fgervais/usbarm/Planning/deviceConnected.png

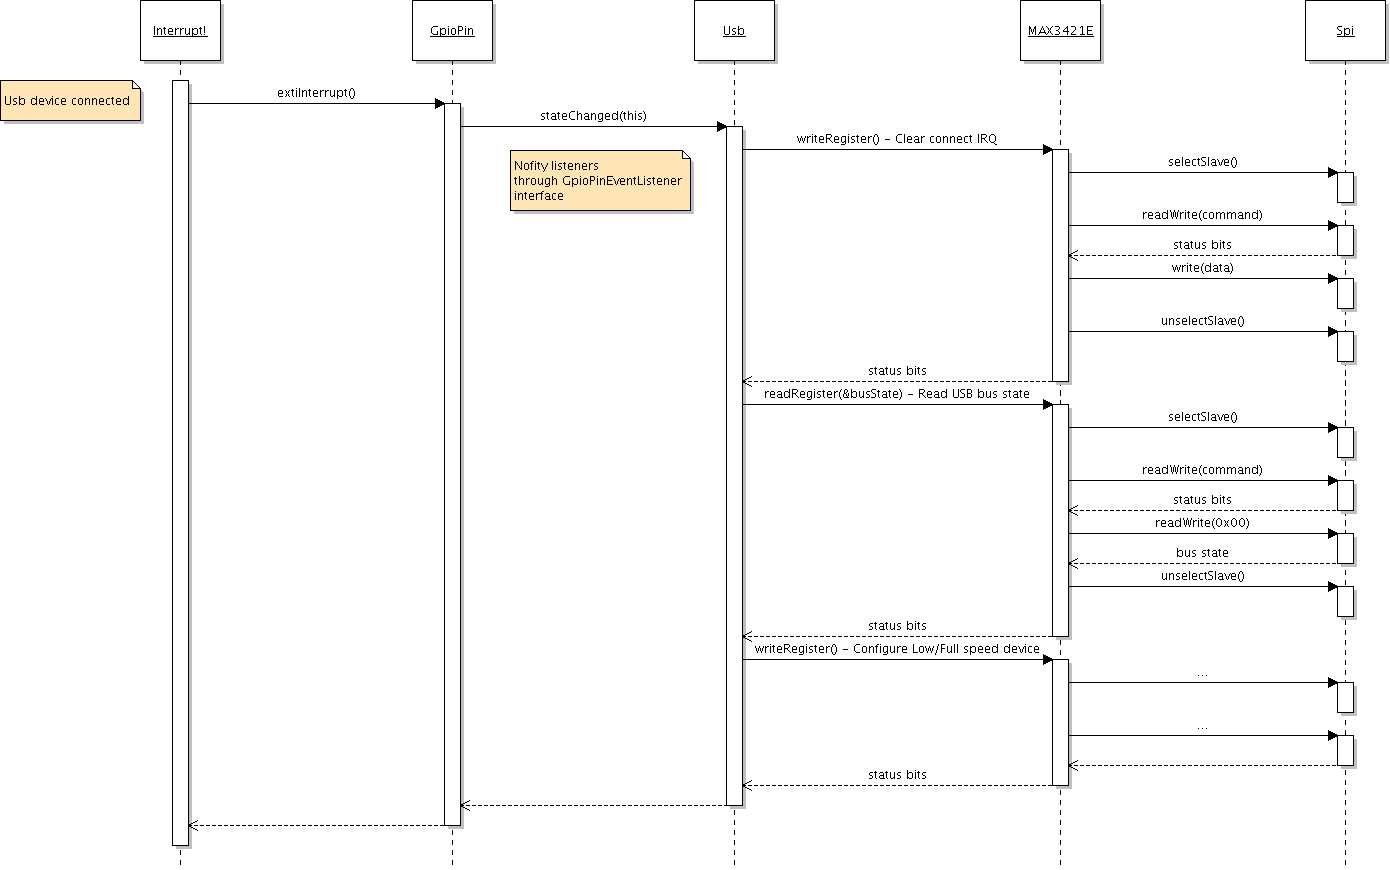
Planning/deviceConnected.png
