fgervais/usbarm/Planning/Framework_layer.png

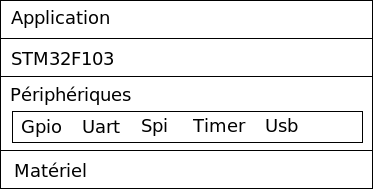
Planning/Framework_layer.png
