fgervais/usbarm/Planning/framework_led.png

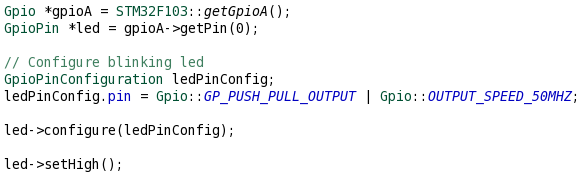
Planning/framework_led.png
