fgervais/usbarm/Planning/gantt-1dec2009.png

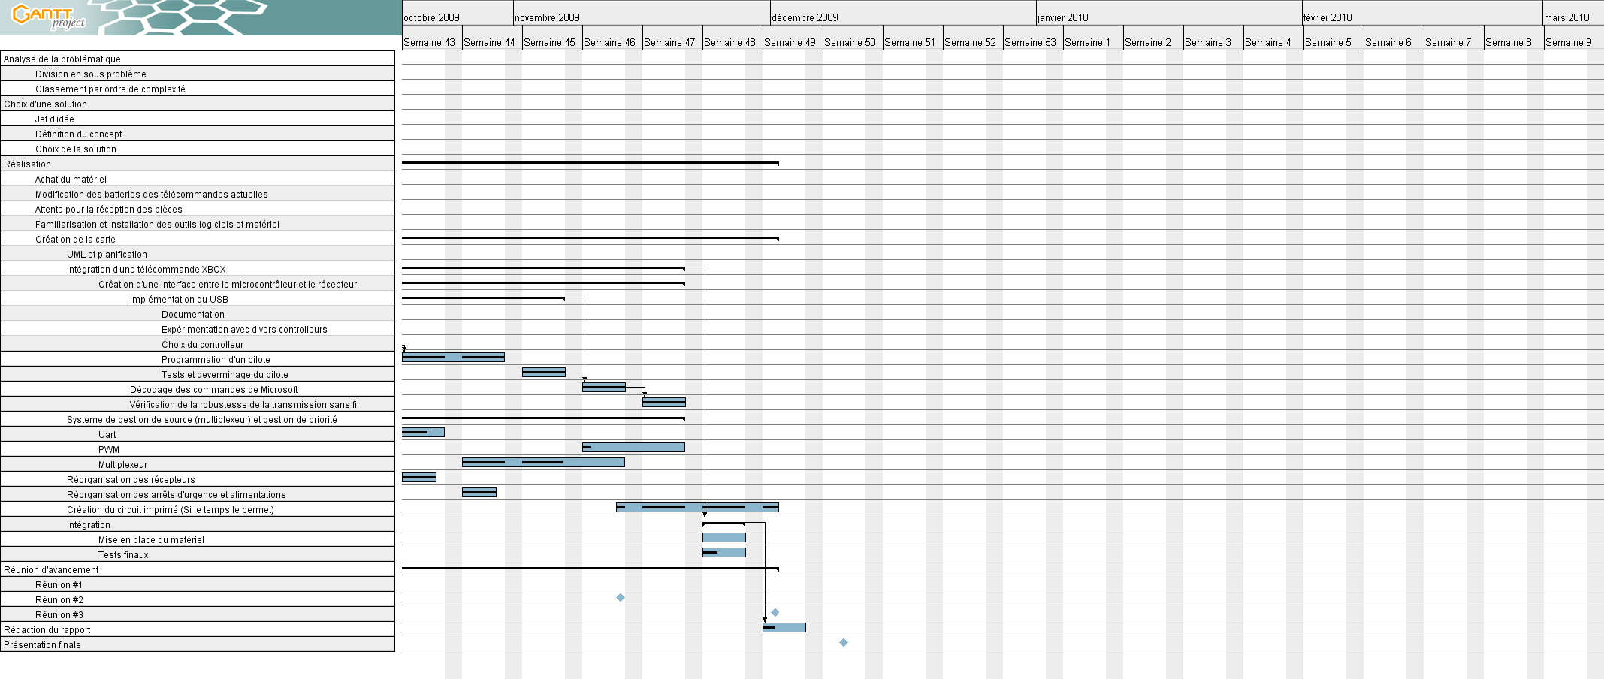
Planning/gantt-1dec2009.png
