fgervais/usbarm/Planning/gantt.png

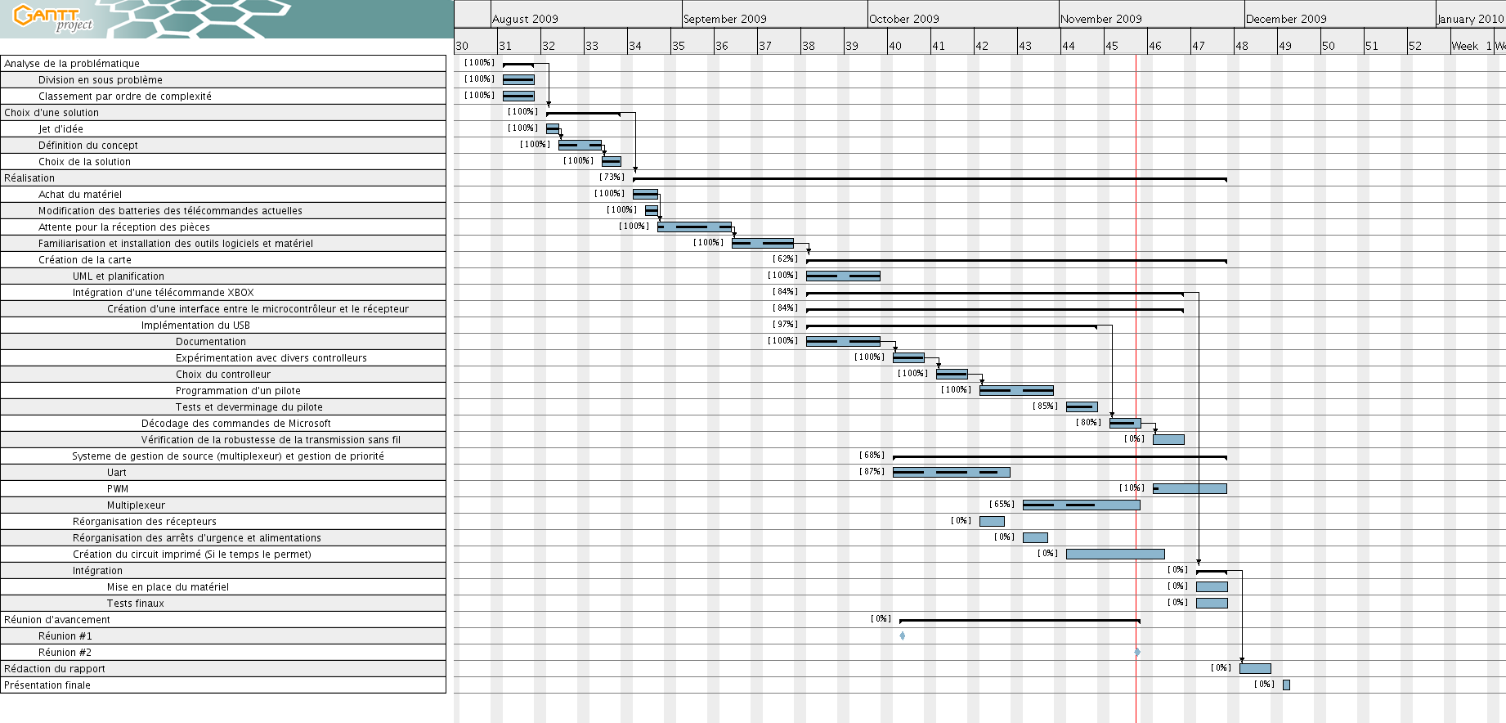
Planning/gantt.png
