fgervais/usbarm/Planning/listenForDevice.png

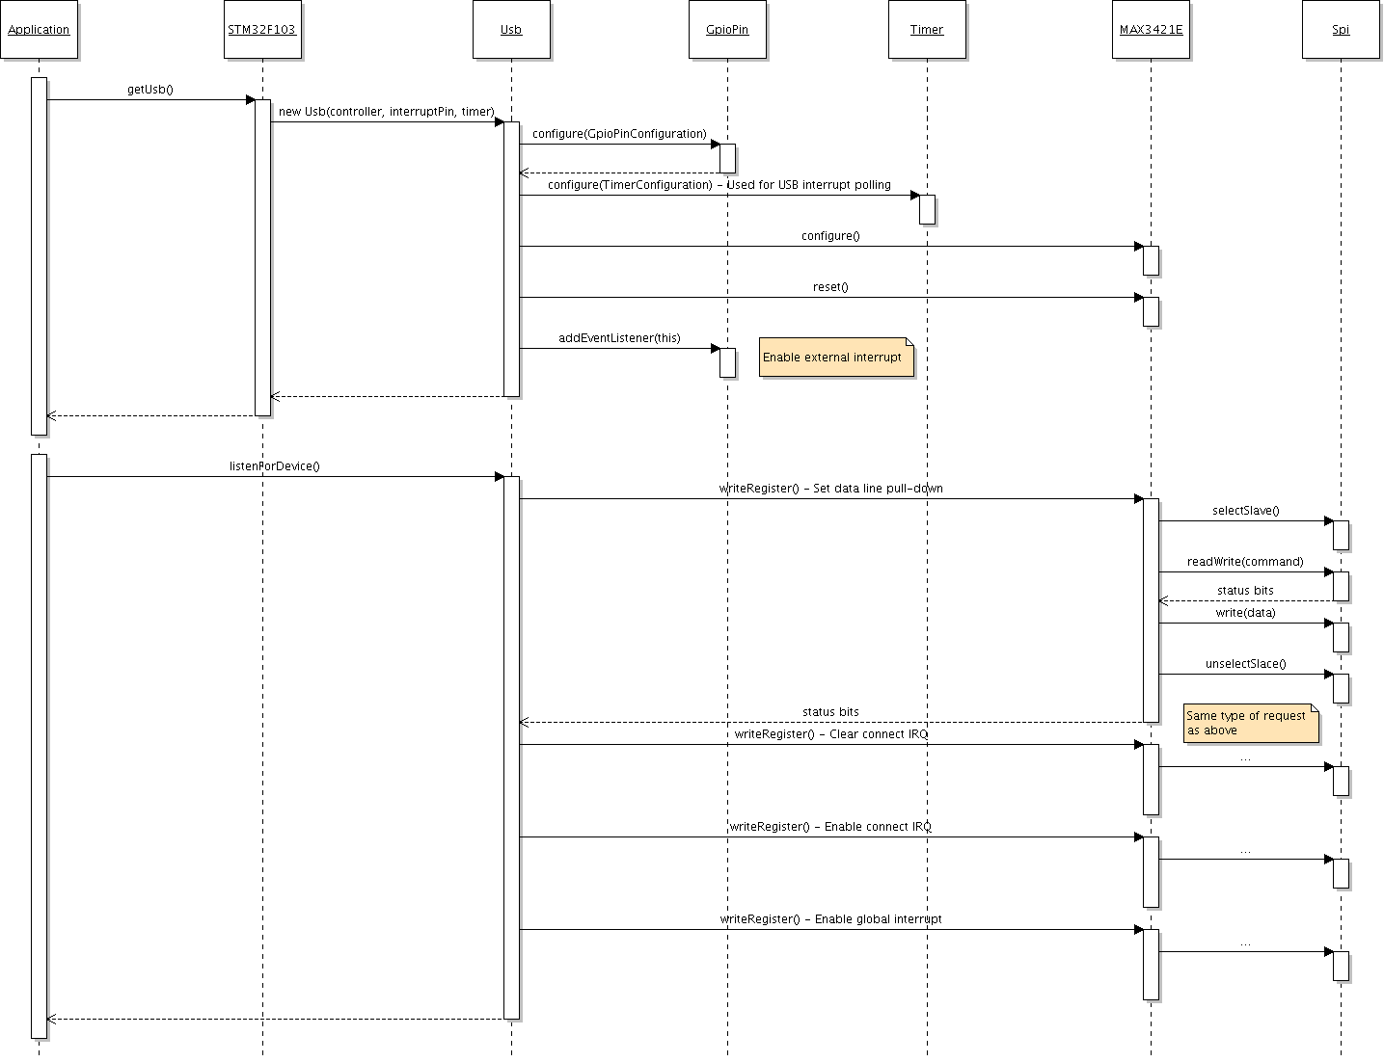
Planning/listenForDevice.png
