fgervais/usbarm/Planning/NES-i-Xbox-360-495x367.jpg

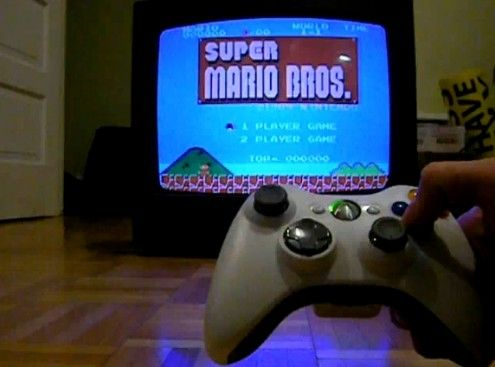
Planning/NES-i-Xbox-360-495x367.jpg
