fgervais/usbarm/Planning/timer_eventlistener.png

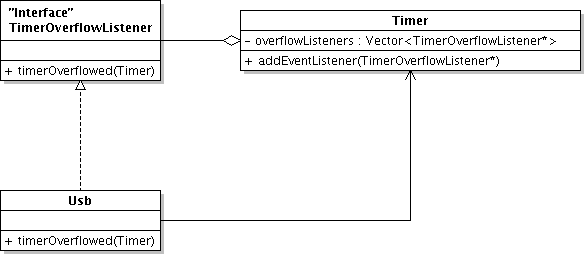
Planning/timer_eventlistener.png
