fgervais/usbarm/Planning/UML.violet.png

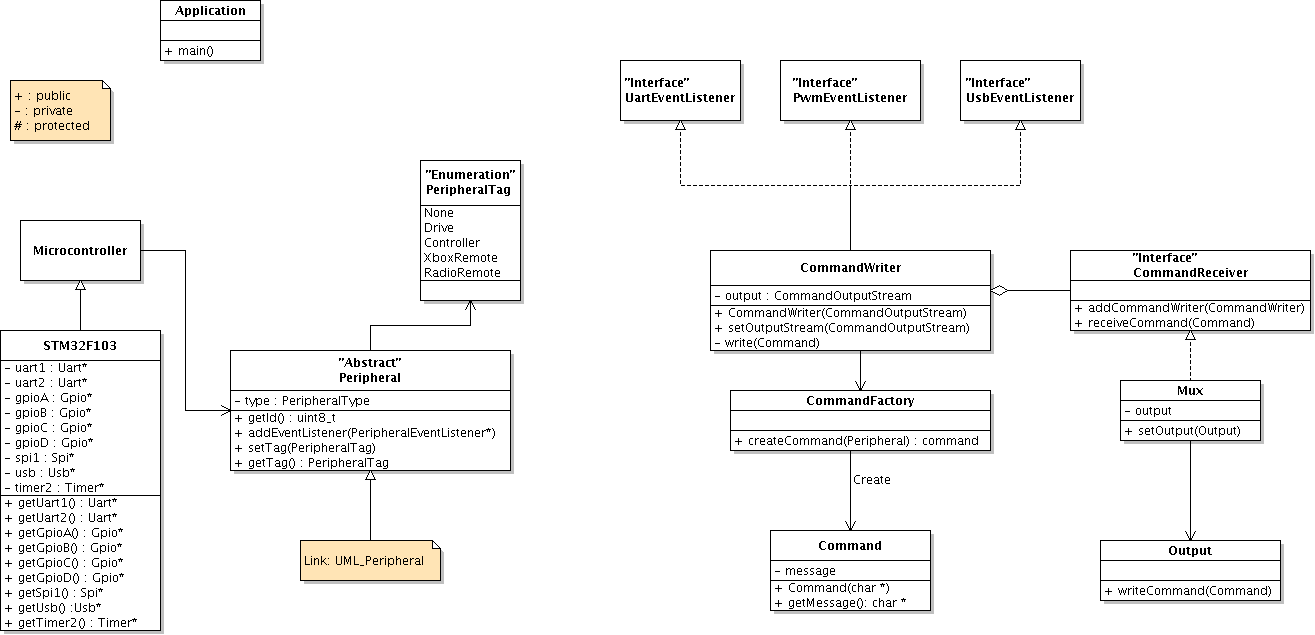
Planning/UML.violet.png
