fgervais/usbarm/Planning/UML_Peripheral.png

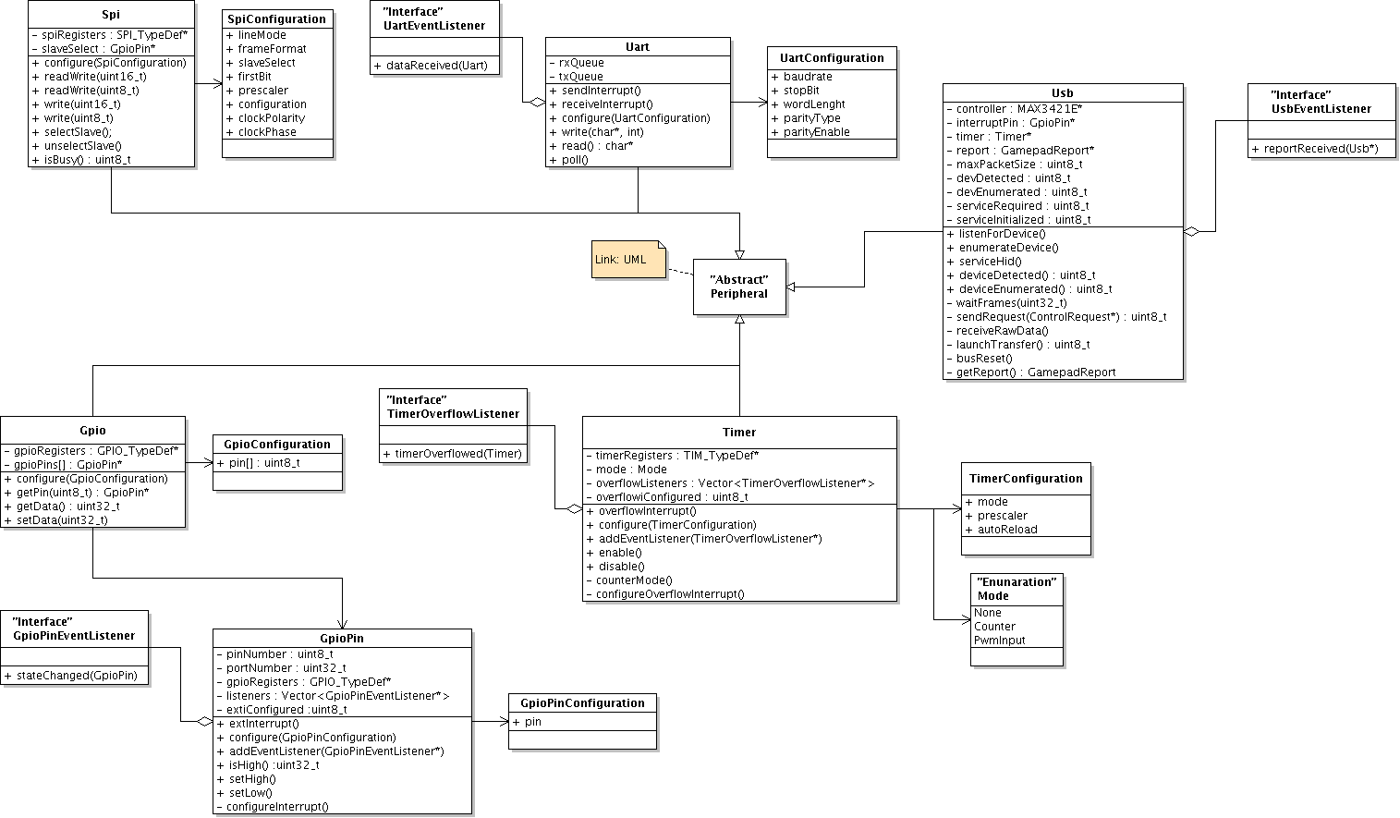
Planning/UML_Peripheral.png
