fgervais/usbarm/Planning/UML_USB.png

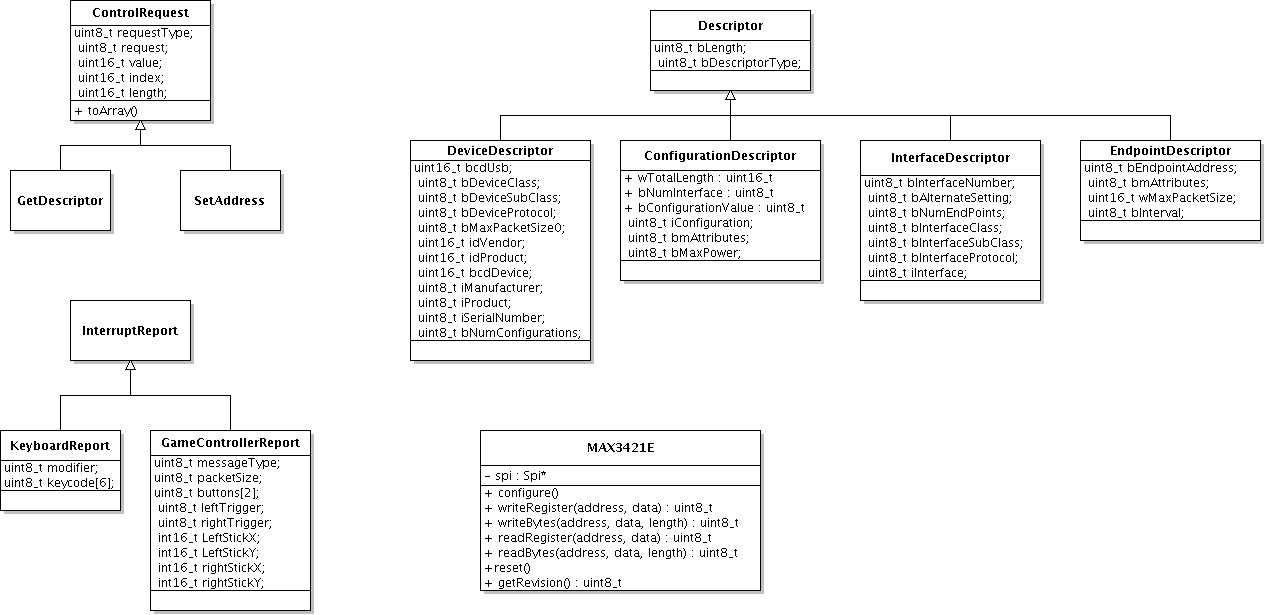
Planning/UML_USB.png
