fgervais/usbarm/Planning/USB_layer.png

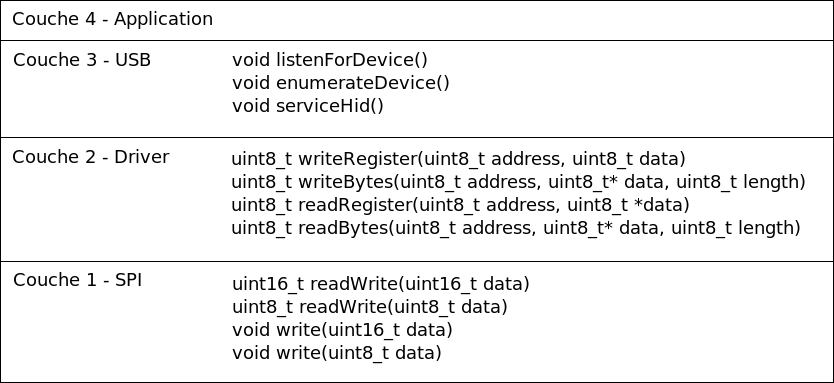
Planning/USB_layer.png
