fgervais/usbarm/Rapport/getReport_time_64.png

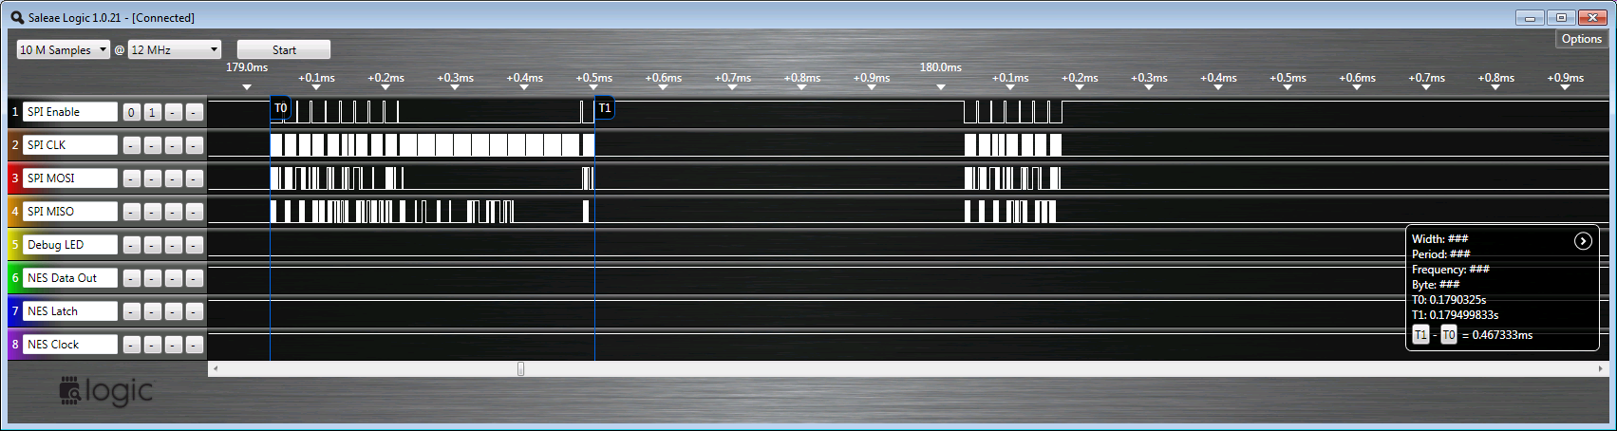
Rapport/getReport_time_64.png
