fgervais/usbarm/Rapport/getReport_time_256.png

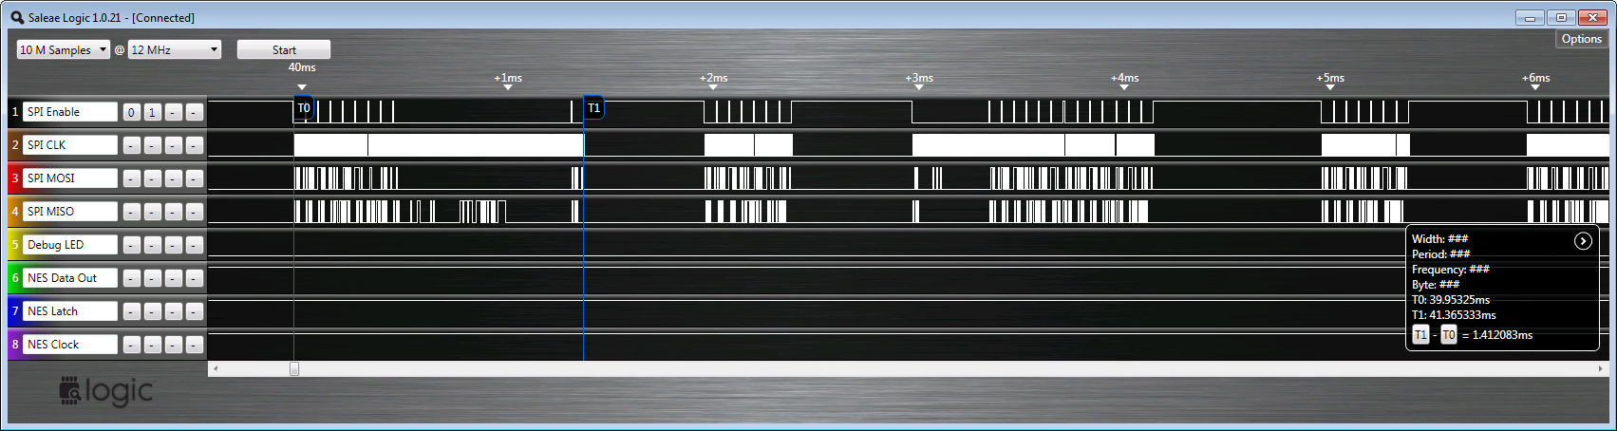
Rapport/getReport_time_256.png
