fgervais/usbarm/Rapport/getReport_time_analysis3.png

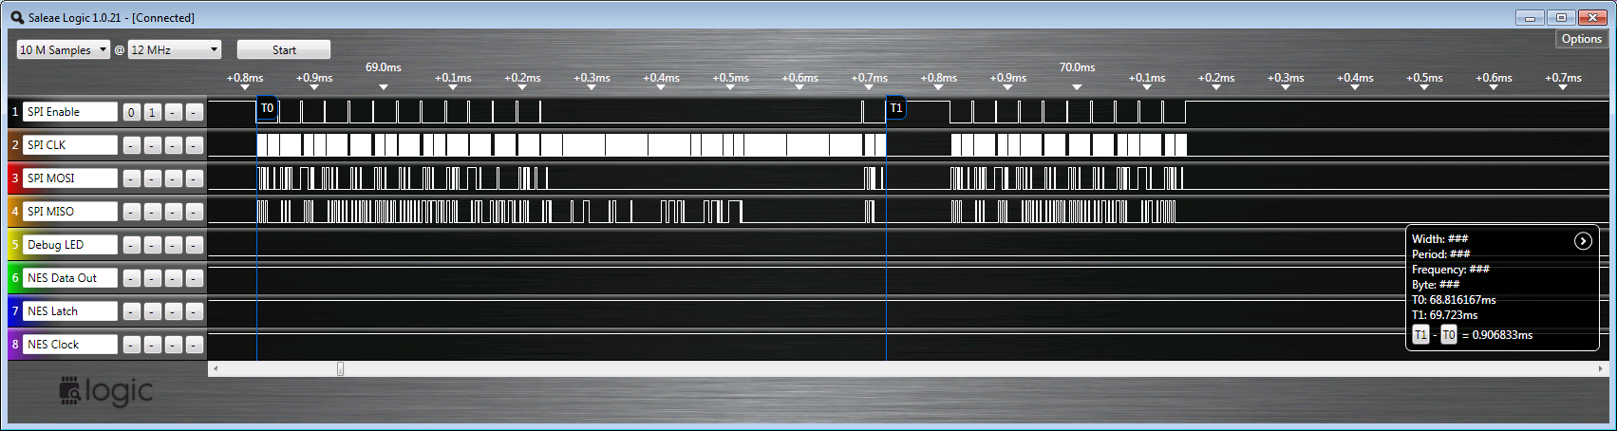
Rapport/getReport_time_analysis3.png
