fgervais/usbarm/Rapport/images/41DaZn46LVL._SL500_AA280_.jpg

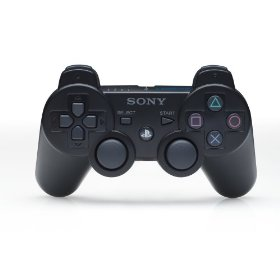
Rapport/images/41DaZn46LVL._SL500_AA280_.jpg
