fgervais/usbarm/Rapport/images/CapraPowerPointbgCapra.png

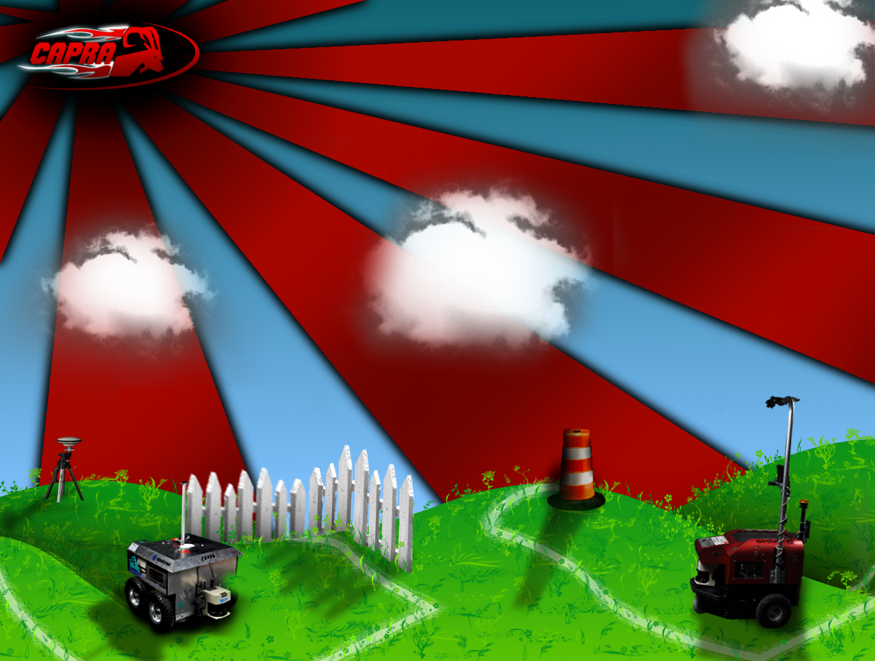
Rapport/images/CapraPowerPointbgCapra.png
