fgervais/usbarm/Rapport/images/CapraPowerPointFront.png

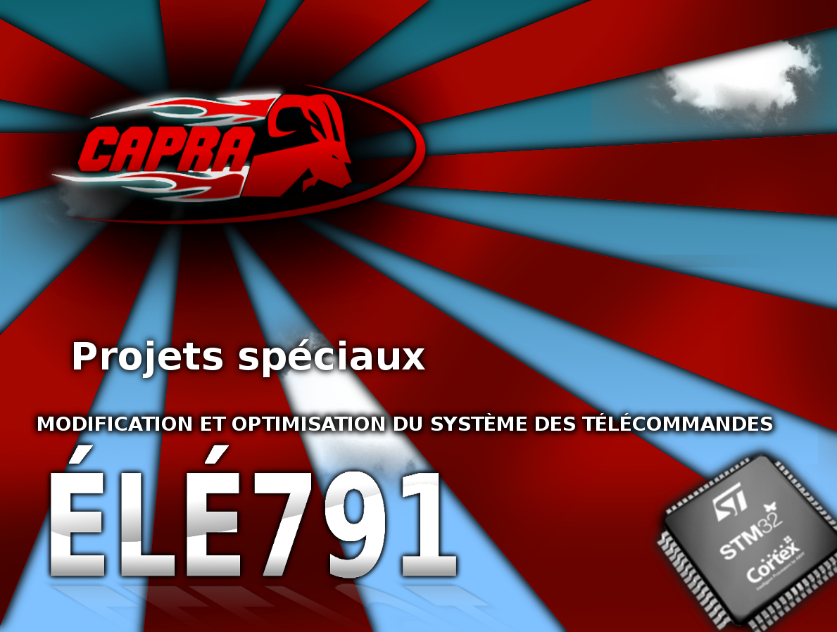
Rapport/images/CapraPowerPointFront.png
