fgervais/usbarm/Rapport/images/certified-hi-speed-usb.jpg

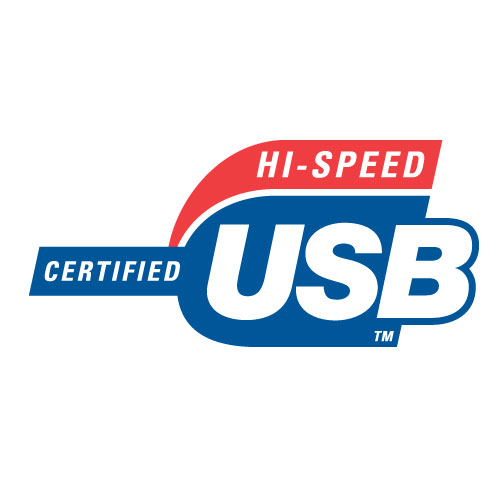
Rapport/images/certified-hi-speed-usb.jpg
