fgervais/usbarm/Rapport/images/RF remote.png

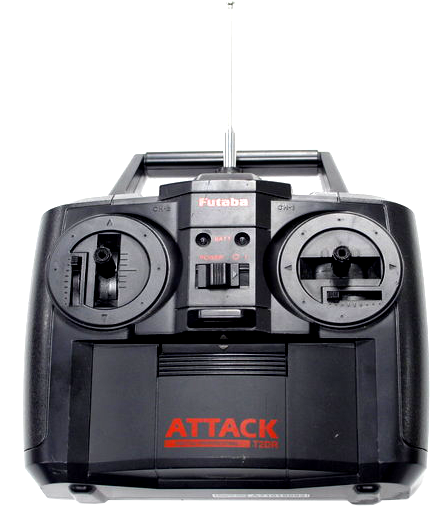
Rapport/images/RF remote.png
