fgervais/usbarm/Refrence/ET-Stamp_stm32_schematic.png

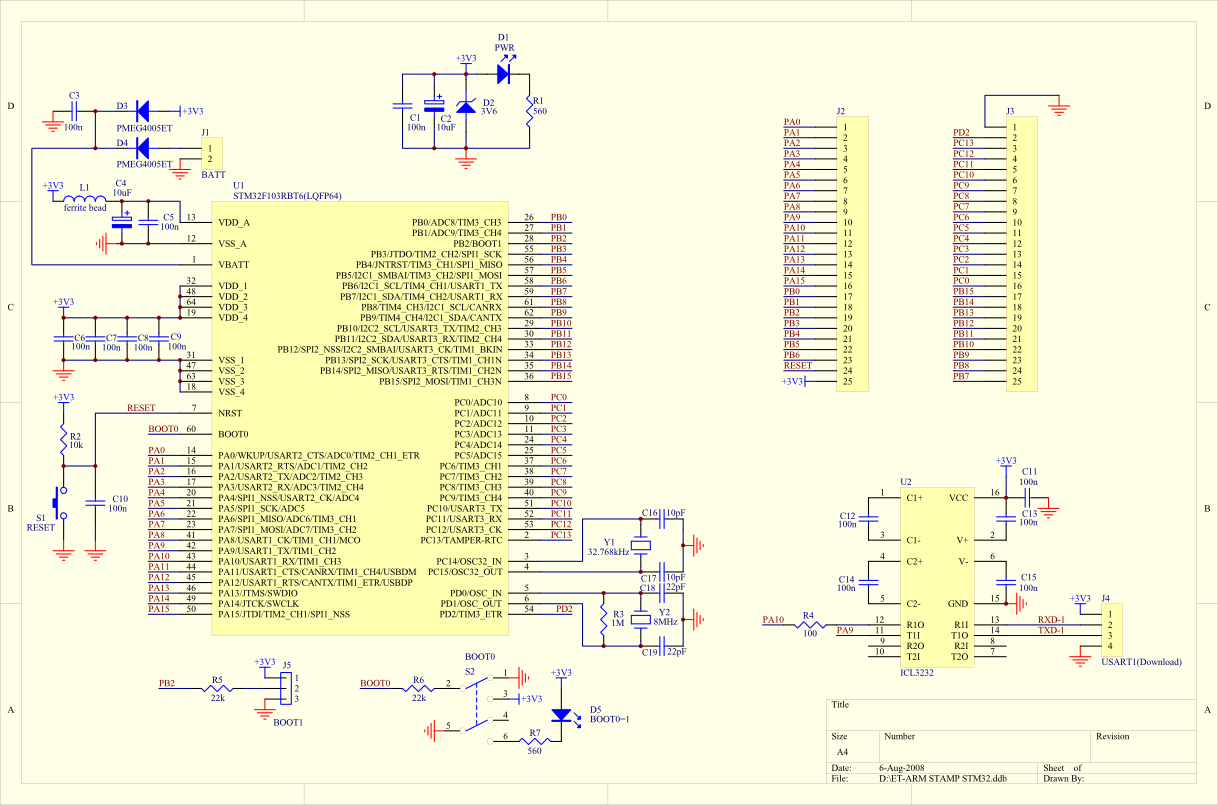
Refrence/ET-Stamp_stm32_schematic.png
