fgervais/usbarm/Pcb/pieces/DB9femelle.pdf

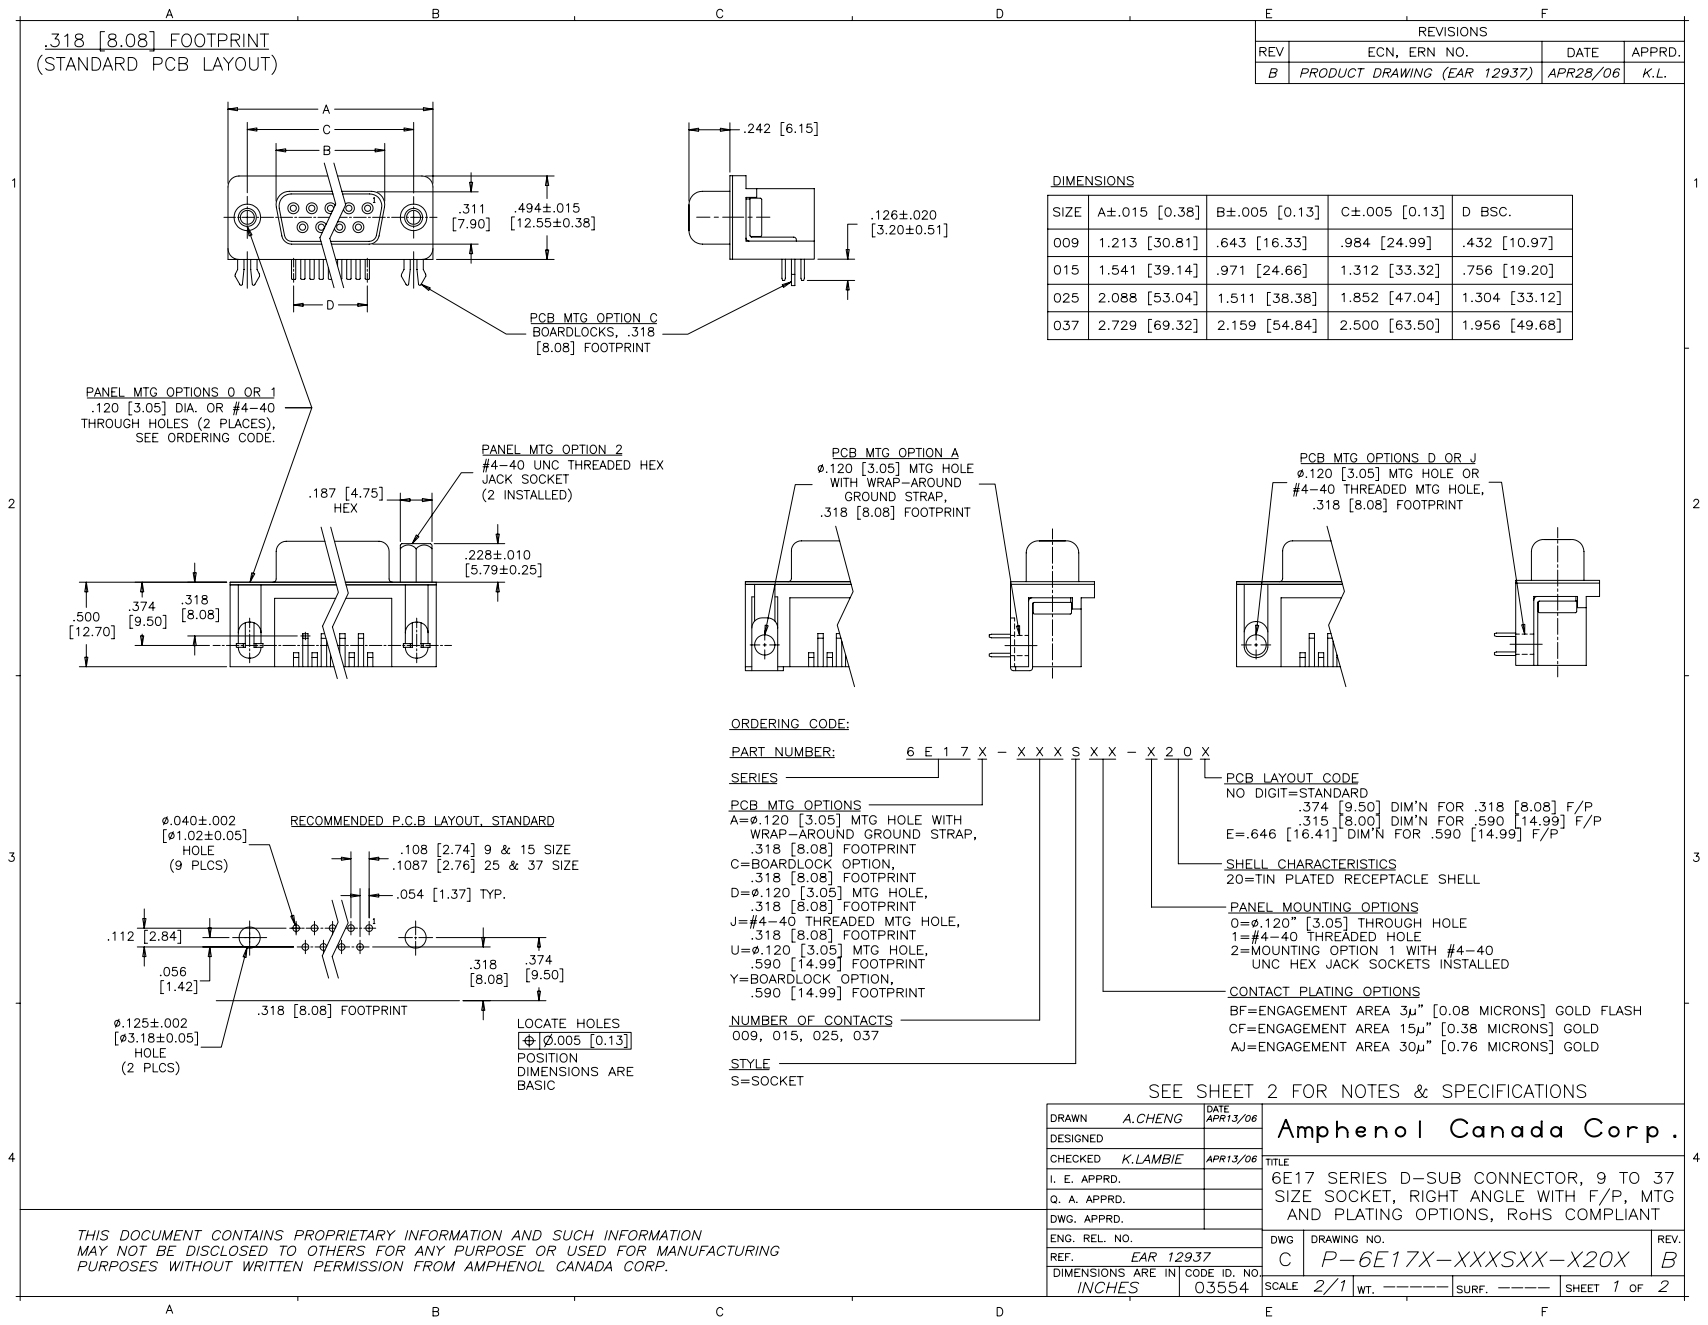
[picture p66: page 1]

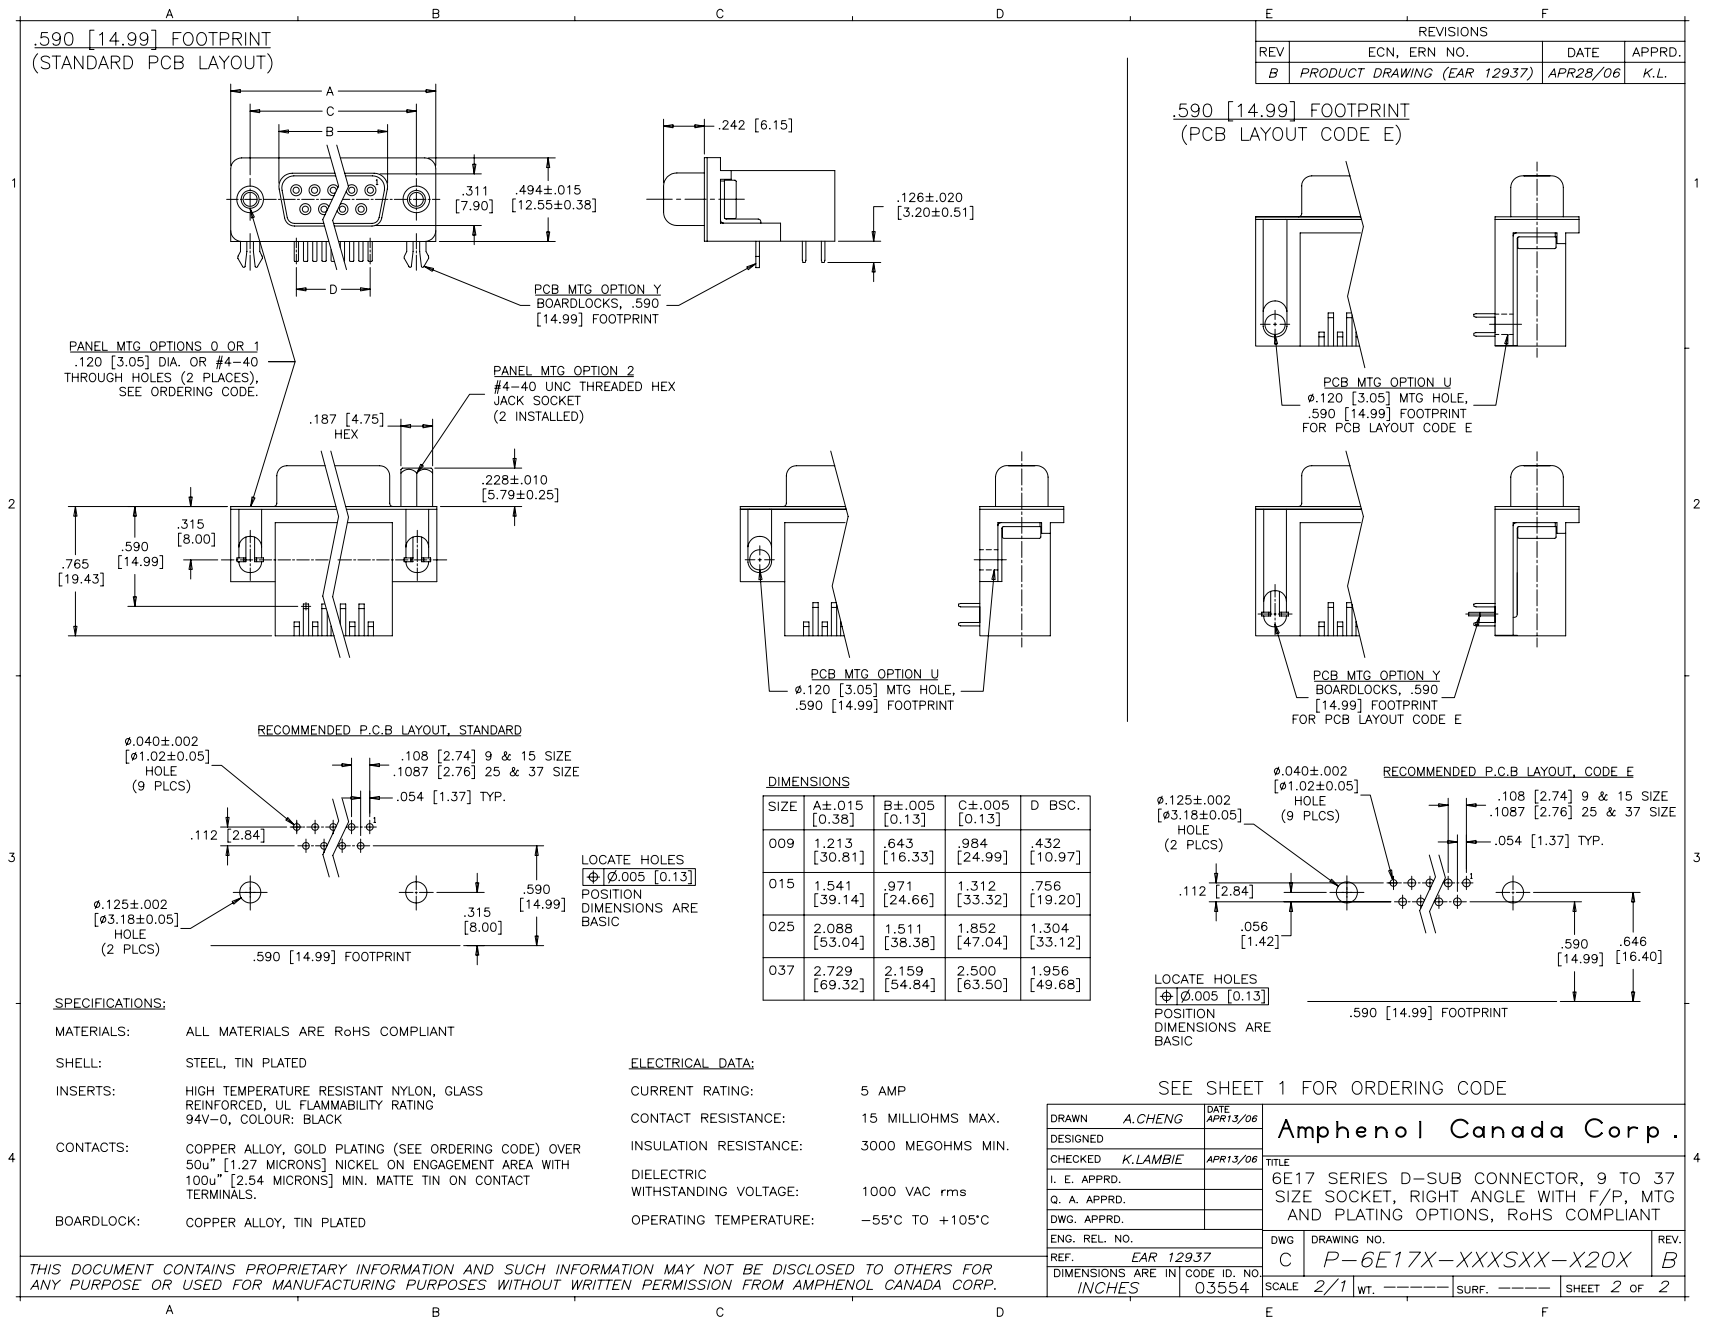
[picture p67: page 2]
