fgervais/usbarm/Microcontroller.h

/*
 * Microcontroller.h
 *
 *  Created on: 2009-09-29
 *      Author: oex
 */

#ifndef MICROCONTROLLER_H_
#define MICROCONTROLLER_H_

class Uart;
class Gpio;

class Microcontroller {
public:
	Microcontroller();
	virtual ~Microcontroller();
};

#endif /* MICROCONTROLLER_H_ */
