fgervais/usbarm/peripheral/Peripheral.h

/*
 * Peripheral.h
 *
 *  Created on: 2009-09-29
 *      Author: oex
 */

#ifndef PERIPHERAL_H_
#define PERIPHERAL_H_

#include "Microcontroller.h"

#include <stdint.h>
#include "Vector.h"

class PeripheralEventListener;

class Peripheral {
public:
	enum PeripheralTag { None =0, Drive, Controller, XboxRemote, RadioRemote };
	Peripheral();
	Peripheral(uint8_t id);
	virtual ~Peripheral();

	uint8_t getId() { return id; }
	void addEventListener(PeripheralEventListener *listener);
	void setTag(PeripheralTag tag);
	PeripheralTag getTag() { return tag; }

private:
	uint8_t id;
	PeripheralTag tag;
	Vector<PeripheralEventListener*> listeners;


protected:
	void notify();
};

#endif /* PERIPHERAL_H_ */
