fgervais/usbarm/MAX3421E.cpp

/*
 * MAX3421E.cpp
 *
 *  Created on: Oct 13, 2009
 *      Author: fgervais
 */

#include "MAX3421E.h"

#include "Spi.h"
#include "SpiConfiguration.h"

MAX3421E::MAX3421E(Spi *spi) {
	this->spi = spi;

	// Configure SPI according to MAX3421E datasheet (mode 0,0).
	SpiConfiguration spiConfig;
	spiConfig.lineMode 		= Spi::FULL_DUPLEX_2LINES;
	spiConfig.frameFormat 	= Spi::FRAME_8BITS;
	spiConfig.slaveSelect 	= Spi::SOFTWARE_SLAVESELECT;
	spiConfig.firstBit 		= Spi::MSB_FIRST;
	spiConfig.prescaler 	= Spi::CLOCK_PRESCALER_128;
	spiConfig.configuration = Spi::MASTER;
	spiConfig.clockPolarity = Spi::CLOCK_POLARITY_LOW;
	spiConfig.clockPhase 	= Spi::CLOCK_PHASE_EDGE1;

	spi->configure(spiConfig);
}

MAX3421E::~MAX3421E() {

}

/**
 * @brief Write data to the specified register address.
 * @param address Address of the register to write to.
 * @param data Data to write to the register.
 * @return Status bits.
 */
uint8_t MAX3421E::writeRegister(uint8_t address, uint8_t data) {
	return writeBytes(address, &data, 1);
}

/**
 * @brief Write multiple bytes to the MAX3421E.
 *
 * Depending of the specified register address. The MAX3421E is
 * going to have specific behavior. For example, multiple access
 * to the FIFOs freeze the internal MAX3421E register address.
 *
 * @see MAX3421E datasheet for more informations.
 *
 * @param address Register address of the first byte.
 * @param data Array of bytes to write.
 * @param length Number of bytes in the array.
 * @return Status bits.
 */
uint8_t MAX3421E::writeBytes(uint8_t address, uint8_t *data, uint8_t length) {
	uint8_t status;

	// For more information on command format, see MAX3421E datasheet
	uint8_t command = address << 3;
	// Direction bit = 1 (write)
	command |= 0x02;

	spi->selectSlave();
	// While the command is clocked in, the status bits are clocked out
	status = spi->readWrite(command);

	for(uint8_t i=0; i<length; i++) {
		spi->write(data[i]);
	}

	// Wait until spi is finished with the transmission
	while(spi->isBusy());
	spi->unselectSlave();

	return status;
}

/**
 * @brief Read a register.
 * @param address Address of the register to read.
 * @param data Pointer used to return the register value.
 * @return Status bits.
 */
uint8_t MAX3421E::readRegister(uint8_t address, uint8_t *data) {
	return readBytes(address, data, 1);
}

/**
 * @brief Read multiple bytes of the MAX3421E.
 * @param address Register address of the first byte.
 * @param data Array used to return the bytes read.
 * Note: Enough memory must be allocated for "length" elements.
 *
 * @param length Number of byte to read.
 * @return Status bits.
 */
uint8_t MAX3421E::readBytes(uint8_t address, uint8_t *data, uint8_t length) {
	uint8_t status;

	// For more information on command format, see MAX3421E datasheet
	uint8_t command = address << 3;

	spi->selectSlave();
	// While the command is clocked in, the status bits are clocked out
	status = spi->readWrite(command);

	for(uint8_t i=0; i<length; i++) {
		data[i] = spi->readWrite((uint8_t)0x00);
	}

	// Wait until spi is finished with the transmission
	while(spi->isBusy());
	spi->unselectSlave();

	return status;
}

void MAX3421E::configure() {
	// Set the controller in full duplex and positive edge interrupt
	writeRegister(PINCTL, PINCTL_FDUPSPI | PINCTL_POSINT);
}

void MAX3421E::reset() {
	uint8_t usbirq;

	writeRegister(USBCTL, USBCTL_CHIPRES);
	writeRegister(USBCTL, 0x00);
	// Wait until the oscillator and PLL stabilize
	do {
		readRegister(USBIRQ, &usbirq);
	} while(!(usbirq & USBIRQ_OSCOKIRQ));
}

uint8_t MAX3421E::getRevision() {
	uint8_t revision = 0;
	readRegister(REVISION, &revision);

	return revision;
}
