fgervais/usbarm/CommandWriter.cpp

/*
 * CommandWriter.cpp
 *
 *  Created on: 2009-09-29
 *      Author: oex
 */

#include "CommandWriter.h"

void CommandWriter::setOutput() {
	this->output = output;
}

void CommandWriter::write(Command *command) {

}

CommandWriter::CommandWriter() {


}

CommandWriter::~CommandWriter() {

}
