fgervais/usbarm/Mux.cpp

/*
 * Mux.cpp
 *
 *  Created on: 2009-09-29
 *      Author: oex
 */

#include "Mux.h"

void Mux::setOutput(Output* output) {
	this->output = output;
}

void Mux::addCommandWriter() {

}
void Mux::receiveCommand() {

}


Mux::Mux() {


}

Mux::~Mux() {

}
