fgervais/usbarm/CommandFactory.cpp

/*
 * CommandFactory.cpp
 *
 *  Created on: 2009-09-29
 *      Author: oex
 */

#include "CommandFactory.h"


Command* CommandFactory::createCommand(Uart *uart) {
	Command *tmpCommand;

	// the uart that we are working with is plugged to the controller (id 1)
	//if (uart->getId() == 1)
	if (uart->getTag() == Peripheral::Controller)
	{
		controllerBuffer[controllerIndex] = uart->read();
		if (controllerBuffer[controllerIndex] == '\r')
		{
			tmpCommand = new Command(controllerBuffer, controllerIndex+1);
			controllerIndex = 0;
		}
		else
			controllerIndex++;

	}
	// if the uart that we receive is the Drive (id 2)
	//if (uart->getId() == 2)
	else if (uart->getTag() == Peripheral::Drive)
	{
		driveBuffer[driveIndex] = uart->read();
		if (driveBuffer[driveIndex] == '\r')
		{
			tmpCommand = new Command(driveBuffer, driveIndex+1);
			driveIndex = 0;
		}
		else
			driveIndex++;
	}


	return tmpCommand;
}
Command* CommandFactory::createCommand(Usb *usb) {
	Command *tmpCommand;
	char test[9] = "!B77";

	tmpCommand = new Command(test,4);
	return new Command(test,4);
}
Command* CommandFactory::createCommand(Timer *timer) {
	Command *tmpCommand;
	char test[9] = "!B77";

	tmpCommand = new Command(test,4);
	return new Command(test,4);
}

CommandFactory::CommandFactory() {
	controllerIndex = 0;
	driveIndex = 0;
}

CommandFactory::~CommandFactory() {

}
