fgervais/usbarm/CommandReceiver.cpp

/*
 * CommandReceiver.cpp
 *
 *  Created on: 2009-09-29
 *      Author: oex
 */

#include "CommandReceiver.h"


CommandReceiver::CommandReceiver() {


}

void CommandReceiver::addCommandWriter() {

}

CommandReceiver::~CommandReceiver() {

}
